bpijls/little-endian/src/react-application/src/img/emotions/anger.jpg

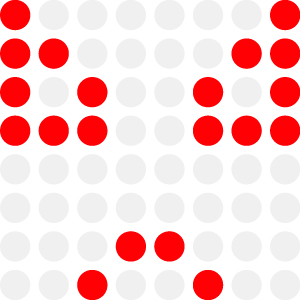
src/react-application/src/img/emotions/anger.jpg
