bpijls/little-endian/src/react-application/src/img/emotions/anger.png

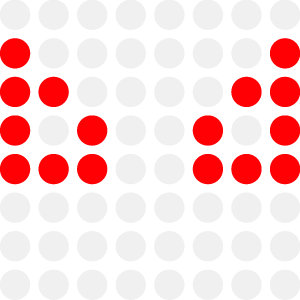
src/react-application/src/img/emotions/anger.png
