bpijls/little-endian/src/react-application/src/img/emotions/disgust.png

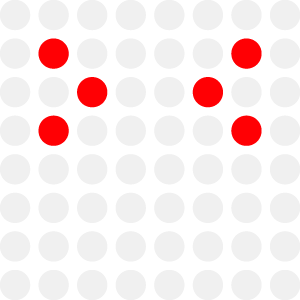
src/react-application/src/img/emotions/disgust.png
