bpijls/little-endian/src/react-application/src/img/emotions/fear.jpg

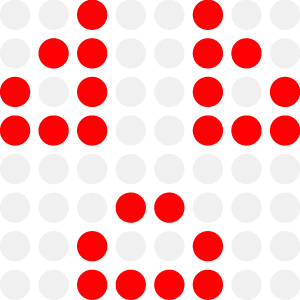
src/react-application/src/img/emotions/fear.jpg
