bpijls/little-endian/src/react-application/src/img/emotions/fear.png

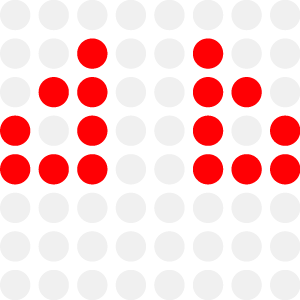
src/react-application/src/img/emotions/fear.png
