bpijls/little-endian/src/react-application/src/img/emotions/happy.jpg

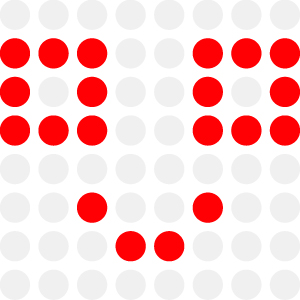
src/react-application/src/img/emotions/happy.jpg
