bpijls/little-endian/src/react-application/src/img/emotions/joy.png

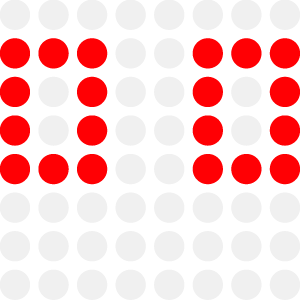
src/react-application/src/img/emotions/joy.png
