bpijls/little-endian/src/react-application/src/img/emotions/surprise.jpg

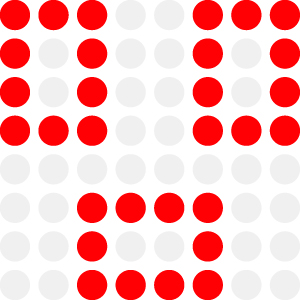
src/react-application/src/img/emotions/surprise.jpg
