bpijls/little-endian/documentation/little-endian-construction-manual.png

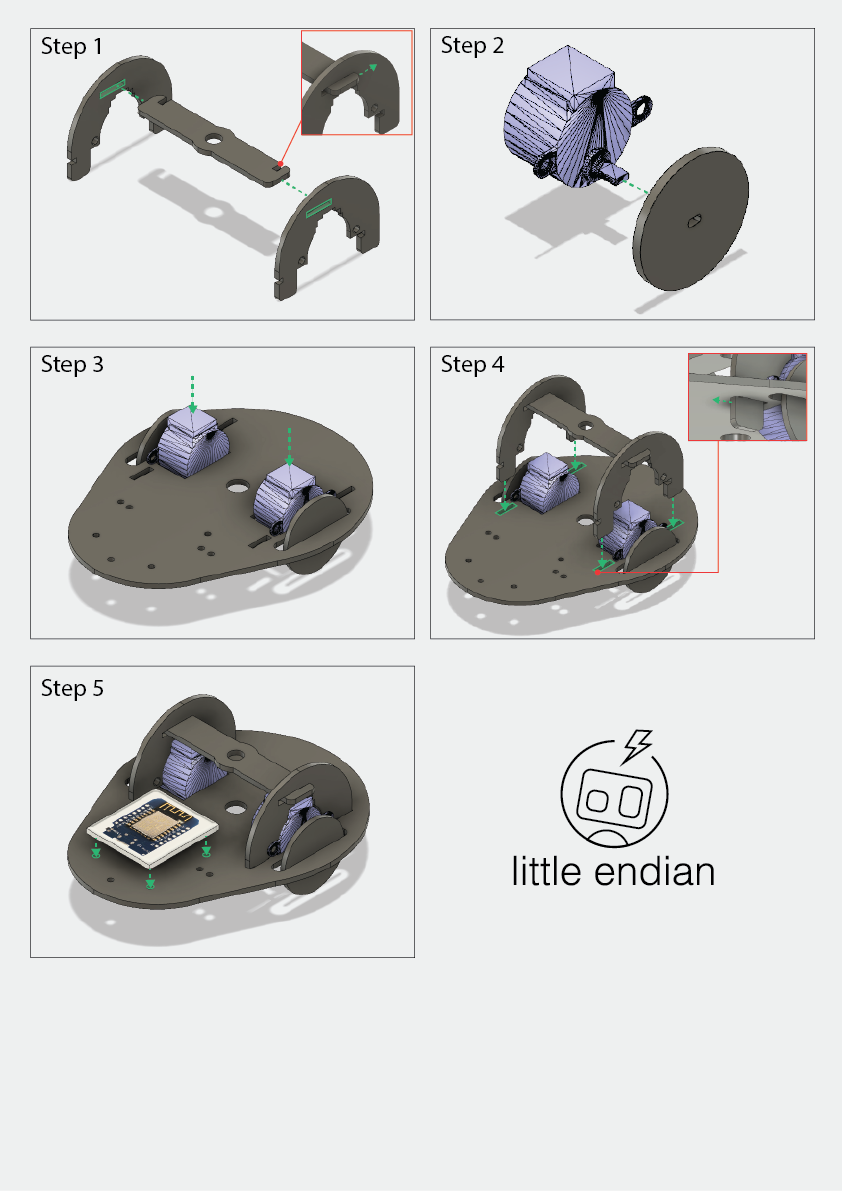
documentation/little-endian-construction-manual.png
